terenceang/BLE_HID/src/platform/user_periph_setup.c

/**
 ****************************************************************************************
 *
 * @file user_periph_setup.c
 *
 * @brief Peripherals initialization - BLE HID gamepad device.
 *
 * Copyright (C) 2015-2023 Renesas Electronics Corporation and/or its affiliates.
 * All rights reserved. Confidential Information.
 *
 ****************************************************************************************
 */

/*
 * INCLUDE FILES
 ****************************************************************************************
 */

#include "user_periph_setup.h"
#include "datasheet.h"
#include "system_library.h"
#include "rwip_config.h"
#include "gpio.h"
#include "syscntl.h"


/*
 * GLOBAL VARIABLE DEFINITIONS
 ****************************************************************************************
 */

/**
 ****************************************************************************************
 * @brief Each application reserves its own GPIOs here.
 ****************************************************************************************
 */

#if DEVELOPMENT_DEBUG

void GPIO_reservations(void)
{
/*
    i.e. to reserve P0_1 as Generic Purpose I/O:
    RESERVE_GPIO(DESCRIPTIVE_NAME, GPIO_PORT_0, GPIO_PIN_1, PID_GPIO);
*/

#if defined (CFG_PRINTF_UART2)
    RESERVE_GPIO(UART2_TX, UART2_TX_PORT, UART2_TX_PIN, PID_UART2_TX);
#endif

    RESERVE_GPIO(SNES_LATCH, SNES_LATCH_PORT, SNES_LATCH_PIN, PID_GPIO);
    RESERVE_GPIO(SNES_CLOCK, SNES_CLOCK_PORT, SNES_CLOCK_PIN, PID_GPIO);
    RESERVE_GPIO(SNES_DATA, SNES_DATA_PORT, SNES_DATA_PIN, PID_GPIO);

#if defined (CFG_SPI_FLASH_ENABLE) && !defined (__DA14586__)
    RESERVE_GPIO(SPI_EN, SPI_EN_PORT, SPI_EN_PIN, PID_SPI_EN);
    RESERVE_GPIO(SPI_CLK, SPI_CLK_PORT, SPI_CLK_PIN, PID_SPI_CLK);
    RESERVE_GPIO(SPI_DO, SPI_DO_PORT, SPI_DO_PIN, PID_SPI_DO);
    RESERVE_GPIO(SPI_DI, SPI_DI_PORT, SPI_DI_PIN, PID_SPI_DI);
#endif
}

#endif

void set_pad_functions(void)
{
/*
    i.e. to set P0_1 as Generic purpose Output:
    GPIO_ConfigurePin(GPIO_PORT_0, GPIO_PIN_1, OUTPUT, PID_GPIO, false);
*/

#if defined (CFG_PRINTF_UART2)
    // Configure UART2 TX pad
    GPIO_ConfigurePin(UART2_TX_PORT, UART2_TX_PIN, OUTPUT, PID_UART2_TX, false);
#endif

#if defined (__DA14586__) && defined (CFG_SPI_FLASH_ENABLE)
    // Disallow spontaneous DA14586 SPI Flash wake-up
    GPIO_ConfigurePin(GPIO_PORT_2, GPIO_PIN_3, OUTPUT, PID_GPIO, true);
#endif

    // SNES controller: LATCH idles low, CLOCK idles high, DATA is an active-low input
    GPIO_ConfigurePin(SNES_LATCH_PORT, SNES_LATCH_PIN, OUTPUT, PID_GPIO, false);
    GPIO_ConfigurePin(SNES_CLOCK_PORT, SNES_CLOCK_PIN, OUTPUT, PID_GPIO, true);
    GPIO_ConfigurePin(SNES_DATA_PORT, SNES_DATA_PIN, INPUT_PULLUP, PID_GPIO, false);

#if defined (CFG_SPI_FLASH_ENABLE) && !defined (__DA14586__)
    GPIO_ConfigurePin(SPI_EN_PORT, SPI_EN_PIN, OUTPUT, PID_SPI_EN, true);
    GPIO_ConfigurePin(SPI_CLK_PORT, SPI_CLK_PIN, OUTPUT, PID_SPI_CLK, false);
    GPIO_ConfigurePin(SPI_DO_PORT, SPI_DO_PIN, OUTPUT, PID_SPI_DO, false);
    GPIO_ConfigurePin(SPI_DI_PORT, SPI_DI_PIN, INPUT, PID_SPI_DI, false);
#endif
}

#if defined (CFG_PRINTF_UART2)
// Configuration struct for UART2
static const uart_cfg_t uart_cfg = {
    .baud_rate = UART2_BAUDRATE,
    .data_bits = UART2_DATABITS,
    .parity = UART2_PARITY,
    .stop_bits = UART2_STOPBITS,
    .auto_flow_control = UART2_AFCE,
    .use_fifo = UART2_FIFO,
    .tx_fifo_tr_lvl = UART2_TX_FIFO_LEVEL,
    .rx_fifo_tr_lvl = UART2_RX_FIFO_LEVEL,
    .intr_priority = 2,
};
#endif

#if defined (CFG_SPI_FLASH_ENABLE)
static const spi_cfg_t spi_cfg = {
    .spi_ms = SPI_MS_MODE,
    .spi_cp = SPI_CP_MODE,
    .spi_speed = SPI_SPEED_MODE,
    .spi_wsz = SPI_WSZ,
    .spi_cs = SPI_CS,
    .cs_pad.port = SPI_EN_PORT,
    .cs_pad.pin = SPI_EN_PIN,
#if defined (__DA14531__)
    .spi_capture = SPI_EDGE_CAPTURE,
#endif
};

static const spi_flash_cfg_t spi_flash_cfg = {
    .chip_size = SPI_FLASH_DEV_SIZE,
};
#endif

void periph_init(void)
{
#if defined (__DA14531__)
    // In Boost mode enable the DCDC converter to supply VBAT_HIGH for the used GPIOs
    // Assumption: The connected external peripheral is powered by 3V
    syscntl_dcdc_turn_on_in_boost(SYSCNTL_DCDC_LEVEL_3V0);
#else
    // Power up peripherals' power domain
    SetBits16(PMU_CTRL_REG, PERIPH_SLEEP, 0);
    while (!(GetWord16(SYS_STAT_REG) & PER_IS_UP));
    SetBits16(CLK_16M_REG, XTAL16_BIAS_SH_ENABLE, 1);
#endif

    // ROM patch
    patch_func();

    // Initialize peripherals
#if defined (CFG_PRINTF_UART2)
    // Initialize UART2
    uart_initialize(UART2, &uart_cfg);
#endif

#if defined (CFG_SPI_FLASH_ENABLE)
    spi_flash_configure_env(&spi_flash_cfg);
    spi_initialize(&spi_cfg);
#endif

    // Set pad functionality
    set_pad_functions();

    // Enable the pads
    GPIO_set_pad_latch_en(true);

}
