terenceang/BLE_HID/src/user_hid.h

/**
 ****************************************************************************************
 *
 * @file user_hid.h
 *
 * @brief Application level (user) interface - BLE HID gamepad device.
 *
 * Copyright (C) 2015-2023 Renesas Electronics Corporation and/or its affiliates.
 * All rights reserved. Confidential Information.
 *
 ****************************************************************************************
 */

#ifndef _USER_HID_H_
#define _USER_HID_H_

/**
 ****************************************************************************************
 * @addtogroup APP
 * @ingroup RICOW
 *
 * @brief
 *
 * @{
 ****************************************************************************************
 */

/*
 * INCLUDE FILES
 ****************************************************************************************
 */

#include "rwble_config.h"
#include "app_task.h"                  // application task
#include "gapc_task.h"                 // gap functions and messages
#include "gapm_task.h"                 // gap functions and messages
#include "app.h"                       // application definitions
#include "co_error.h"                  // error code definitions
#include "arch_wdg.h"

#include "app_callback.h"
#include "app_default_handlers.h"

/*
 * DEFINES
 ****************************************************************************************
 */

/* Duration of timer for connection parameter update request */
#define APP_PARAM_UPDATE_REQUEST_TO         (100)   // 100*10ms = 1sec

/*
 * FUNCTION DECLARATIONS
 ****************************************************************************************
 */

/**
 ****************************************************************************************
 * @brief Application initialization function.
 ****************************************************************************************
 */
void user_app_init(void);

/**
 ****************************************************************************************
 * @brief Advertising function.
 ****************************************************************************************
 */
void user_app_adv_start(void);

/**
 ****************************************************************************************
 * @brief Database initialization complete function.
 ****************************************************************************************
 */
void user_app_on_db_init_complete(void);

/**
 ****************************************************************************************
 * @brief Connection function.
 * @param[in] connection_idx Connection Id index
 * @param[in] param Pointer to GAPC_CONNECTION_REQ_IND message
 ****************************************************************************************
 */
void user_app_connection(uint8_t connection_idx,
                         struct gapc_connection_req_ind const *param);

/**
 ****************************************************************************************
 * @brief Undirect advertising completion function.
 * @param[in] status Command complete event message status
 ****************************************************************************************
 */
void user_app_adv_undirect_complete(uint8_t status);

/**
 ****************************************************************************************
 * @brief Disconnection function.
 * @param[in] param Pointer to GAPC_DISCONNECT_IND message
 ****************************************************************************************
 */
void user_app_disconnect(struct gapc_disconnect_ind const *param);
void user_app_pairing_succeeded(const uint8_t conidx);
void user_app_encrypt_ind(const uint8_t conidx, const uint8_t auth);
void user_app_encrypt_req_ind(const uint8_t conidx, struct gapc_encrypt_req_ind const *param);

/**
 ****************************************************************************************
 * @brief Handles the messages that are not handled by the SDK internal mechanisms.
 * @param[in] msgid   Id of the message received.
 * @param[in] param   Pointer to the parameters of the message.
 * @param[in] dest_id ID of the receiving task instance.
 * @param[in] src_id  ID of the sending task instance.
 ****************************************************************************************
 */
void user_catch_rest_hndl(ke_msg_id_t const msgid,
                          void const *param,
                          ke_task_id_t const dest_id,
                          ke_task_id_t const src_id);

/// @} APP

/// SUOTA status callback (app_suotar_cb in user_callback_config.h)
void user_ota_status_change(const uint8_t suotar_event);

#endif // _USER_HID_H_
